willowec/lightwand/inc/neopixels.h

/*
Functions for controlling neopixel arrays
*/
#ifndef NEOPIXEL
#define NEOPIXEL

#include "pico/stdlib.h"
#include "pico/rand.h" 
#include "hardware/pio.h"
#include "hardware/clocks.h"
#include "ws2812.pio.h"

#include <stdio.h>


/*
The ws2812 datasheet indicates that 50us must be waited between each set of transmissions. However, I found that for
my use case 200us were needed. A possible explanation is that when pio_sm_is_tx_fifo_empty() returns false, the last 32-bit
message is still being transmitted over the data line. Whatever the case, this works, and we don't need the wand to flicker
particularly fast anyway 
*/
#define WS2812_END_SLEEP_US 200

/* 
For a 15-count RGB neopixel strip:
lights up the full strip as one color
returns the amount of time in microseconds it took to resolve the function
*/
static inline uint64_t put_15_pixels_on_rgb(uint32_t pixel_grb) {
    /*
    pio_sm_put_blocking will always put out 32 bits, but we want to send 24 bit chunks in a
    continuous stream. Therefore, some slightly more complicated looping behaviour is required
    */

    int color_channel = 0; // 0: green, 1: red, 2: blue
    int transmitted_bytes = 0;
    int i;
    uint64_t start_us = time_us_64();

    while(1) {
        uint32_t msg = 0;
        for(i=3; i>=0; i--) {
            // get the next color channel value
            uint8_t color_val = ((pixel_grb >> ((2-color_channel) * 8u)) & 0xff);

            // push the next color channel value onto the transmission message
            msg |= color_val << (i * 8u); 
            color_channel = (color_channel + 1) % 3;
            transmitted_bytes++;
        }

        // transmit the next 32-bit chunk of control data
        pio_sm_put_blocking(pio0, 0, msg);

        if (transmitted_bytes >= 45) {
            // 45 bytes of color data, for 15 pixels, have been transmitted
            break;
        }
    }

    // wait for the tx fifo to drain
    while (!pio_sm_is_tx_fifo_empty(pio0, 0))
        sleep_us(1);

    sleep_us(WS2812_END_SLEEP_US);   

    return time_us_64() - start_us; 
}

/*
For a 15-count RGB neopixel strip:
parses the bits of a 32 bit integer and turns leds on or off based on the bits
returns the amount of time in microseconds it took to resolve the function
*/
static inline uint64_t put_15_pixels_rgb(uint32_t bits, uint32_t color_on, uint32_t color_off)
{
    int color_channel = 0; // 0: green, 1: red, 2: blue
    int transmitted_bytes = 0;
    int i;
    uint64_t start_us = time_us_64();

    uint8_t color_val;

    while(1) {
        uint32_t msg = 0;
        for(i=3; i>=0; i--) {
            // choose whether we are in an "on" or "off" pixel
            if (((bits >> (transmitted_bytes/3)) & 1) == 1)
                color_val = ((color_on >> ((2-color_channel) * 8u)) & 0xff);
            else
                color_val = ((color_off >> ((2-color_channel) * 8u)) & 0xff);

            // push the next color channel value onto the transmission message
            msg |= color_val << (i * 8u); 
            color_channel = (color_channel + 1) % 3;
            transmitted_bytes++;
        }

        // transmit the next 32-bit chunk of control data
        pio_sm_put_blocking(pio0, 0, msg);

        if (transmitted_bytes >= 45) {
            // 45 bytes of color data, for 15 pixels, have been transmitted
            break;
        }
    }

    // wait for the tx fifo to drain
    while (!pio_sm_is_tx_fifo_empty(pio0, 0))
        sleep_us(1);

    sleep_us(WS2812_END_SLEEP_US);    // additional wait so WS2812 knows to finish transaction

    return time_us_64() - start_us; 
}


/* 
For a 15-count RGBW neopixel strip:
lights up the full strip as one color
returns the amount of time in microseconds it took to resolve the function
*/
static inline uint64_t put_15_pixels_on_rgbw(uint32_t pixel_grbw) {
    uint64_t start_us = time_us_64();

    // The code for controlling an RGBW strip is much simpler than for the RGB strips.
    for (int i = 0; i < 15; i++) {
        pio_sm_put_blocking(pio0, 0, pixel_grbw);
    }

    // wait for the tx fifo to drain
    while (!pio_sm_is_tx_fifo_empty(pio0, 0))
        sleep_us(1);

        
    sleep_us(WS2812_END_SLEEP_US);

    return time_us_64() - start_us;
}

/* 
For a 15-count RGBW neopixel strip:
parses the bits of a 32 bit integer and turns leds on or off based on the bits
returns the amount of time in microseconds it took to resolve the function
*/
static inline uint64_t put_15_pixels_rgbw(uint32_t bits, uint32_t color_on, uint32_t color_off) {
    uint64_t start_us = time_us_64();

    // The code for controlling an RGBW strip is much simpler than for the RGB strips.
    for (int i = 0; i < 15; i++) {
        if (((bits >> i) & 1) == 1) {
            pio_sm_put_blocking(pio0, 0, color_on);
        }
        else {
            pio_sm_put_blocking(pio0, 0, color_off);
        }
    }

    // wait for the tx fifo to drain
    while (!pio_sm_is_tx_fifo_empty(pio0, 0))
        sleep_us(1);

        
    sleep_us(WS2812_END_SLEEP_US);

    return time_us_64() - start_us;
}

/*
For a 15-count RGBW neopixel strip:
spits random color data onto the wand (adjusted to be prettier)
    white_mask is and-ed with the white channel of the random pixel color
*/
static inline uint64_t put_15_random_rgbw(uint8_t white_mask) {
    uint64_t start_us = time_us_64();

    for (int i = 0; i < 15; i++) {
        pio_sm_put_blocking(pio0, 0, get_rand_32() & 0xFFFFFF00 | white_mask);
    }

    // wait for the tx fifo to drain
    while (!pio_sm_is_tx_fifo_empty(pio0, 0))
        sleep_us(1);
        
    sleep_us(WS2812_END_SLEEP_US);    

    return time_us_64() - start_us; 
}

// taken from hutscape.github.io. Converts r, g, b, to urgb
static inline uint32_t urgb_u32(uint8_t r, uint8_t g, uint8_t b) {
    return  ((uint32_t)(b) << 0)    |
            ((uint32_t)(r) << 8)    |
            ((uint32_t)(g) << 16);
}

// Converts r, g, b, w, to urgbw
static inline uint32_t urgbw_u32(uint8_t r, uint8_t g, uint8_t b, uint8_t w) {
    return  ((uint32_t)(b) << 8)    |
            ((uint32_t)(r) << 16)    |
            ((uint32_t)(g) << 24)   |
            ((uint32_t)(w) << 0);
}

// sets up the ws2812 controller
void setup_ws2812();

#endif
